melvinmajor/tfe-PiSense/doc/pi4-diagram2.jpg

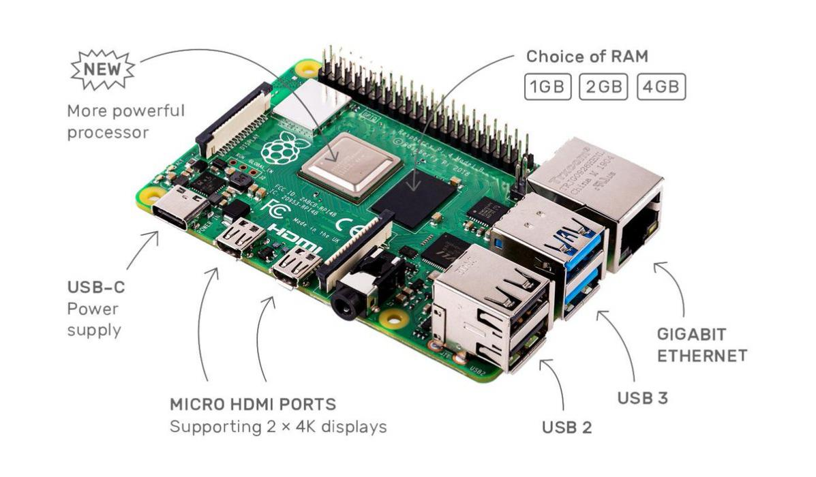
doc/pi4-diagram2.jpg
