melvinmajor/tfe-PiSense/doc/Pictures/3D-box-side1.png

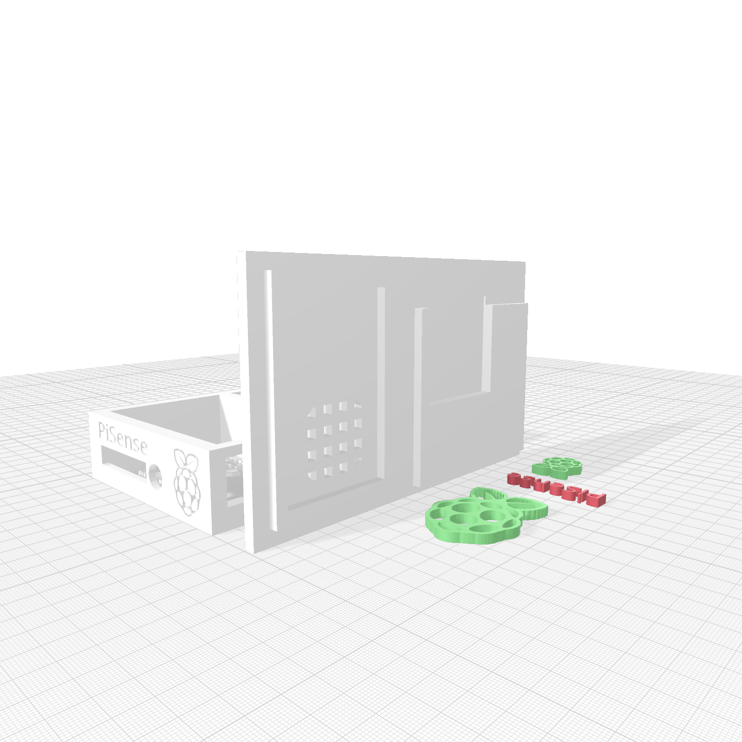
doc/Pictures/3D-box-side1.png
