melvinmajor/tfe-PiSense/doc/Pictures/3D-box-side2.png

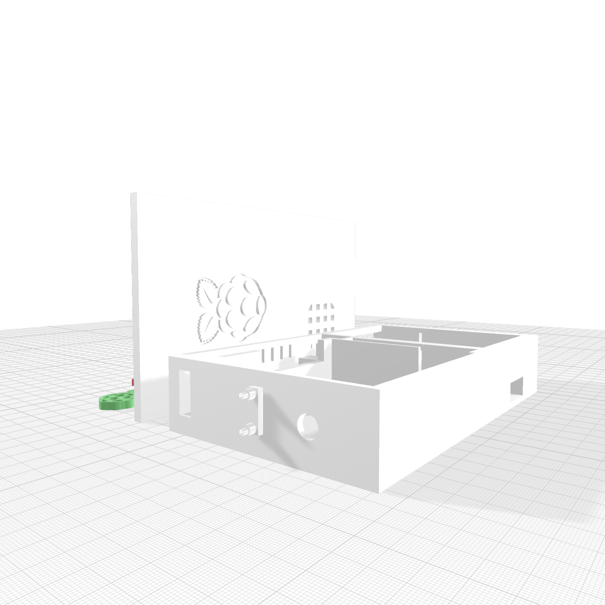
doc/Pictures/3D-box-side2.png
