melvinmajor/tfe-PiSense/doc/Pictures/web-platform-localhost.png

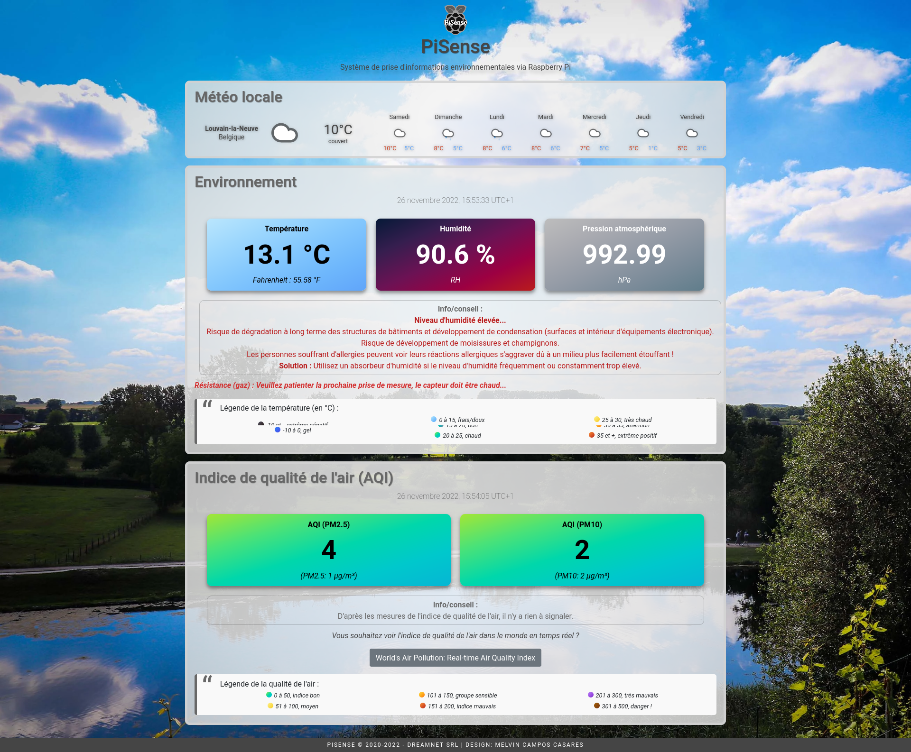
doc/Pictures/web-platform-localhost.png
