melvinmajor/tfe-PiSense/doc/SSL_Labs+Security_headers/securityheaders-june16-camposcasares.be.png

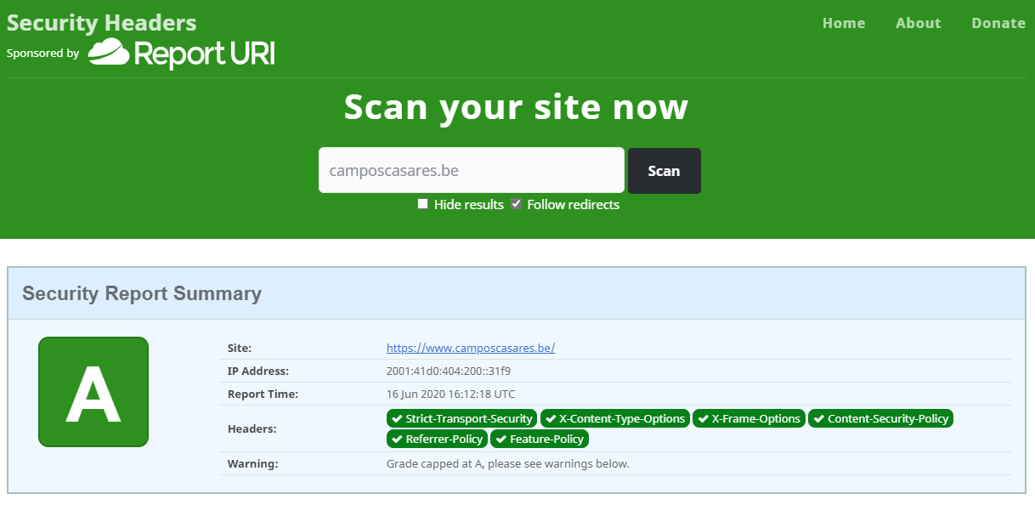
doc/SSL_Labs+Security_headers/securityheaders-june16-camposcasares.be.png
