melvinmajor/tfe-PiSense/localhost-web/assets/images/air-quality-index.webp

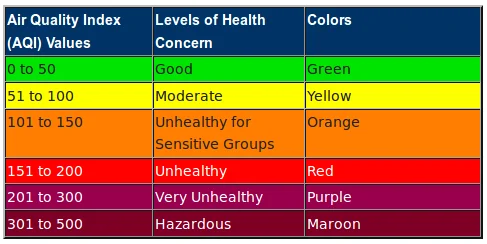
localhost-web/assets/images/air-quality-index.webp
