melvinmajor/tfe-PiSense/localhost-web/assets/images/background-v1.webp

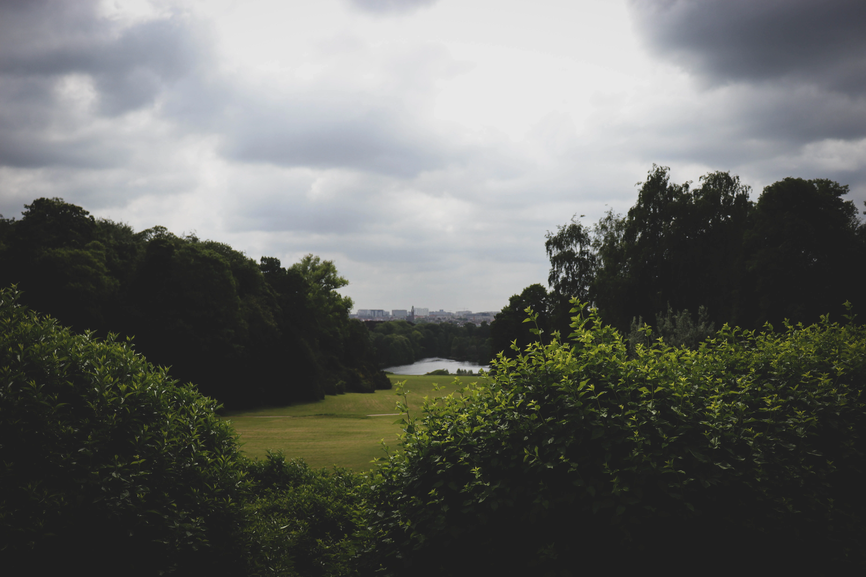
localhost-web/assets/images/background-v1.webp
