melvinmajor/tfe-PiSense/localhost-web/assets/images/background.webp

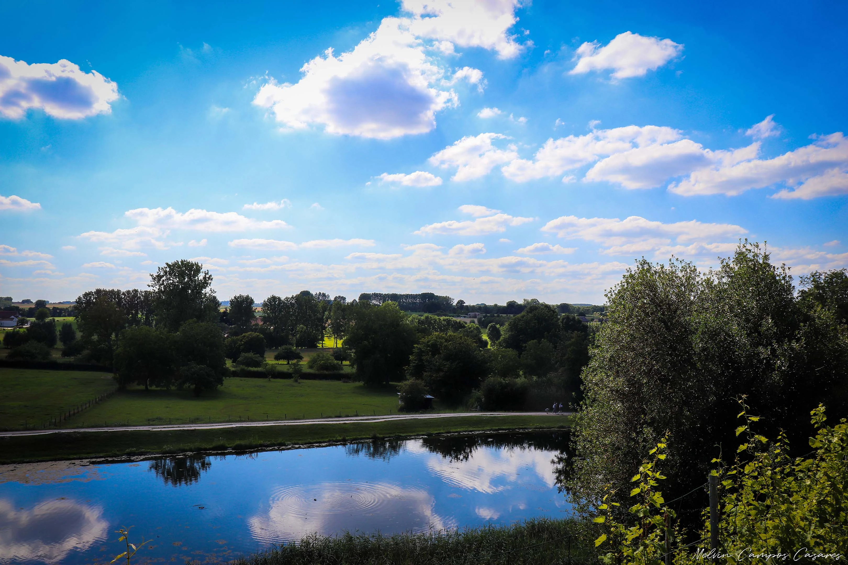
localhost-web/assets/images/background.webp
