melvinmajor/tfe-PiSense/config-manual/Connect-sensors.pdf

# PiSense

## Manual connect sensors on Raspberry Pi devices

## Melvin Campos Casares


9 june 2019

PiSense | 9 june 2019

## Manual - how to connect the different sensors onto Raspberry Pi devices

1 Connect one or multiple sensors onto Raspberry Pi devices | 3
Manual - connect sensors on Raspberry Pi devices | 2

## 1 Connect one or multiple sensors onto Raspberry Pi devices

Currently, this project support the following sensors:

- Nova SDS011: Fine particles in suspension (PM2.5, PM10).
- Bosch BMP280 (based on Adafruit library): temperature and humidity.
- Bosch BME280 (based on Adafruit library): temperature, humidity, atmospheric pressure.
- Bosch BME680 (based on Pimoroni library): temperature, humidity, gas (TVOC, eCO2), atmospheric pressure.

If for any reason you need to connect one of the sensors, here you will find a diagram to help you find out how to process it.

As it’s meant to be connected on Raspberry Pi devices (this project is working on such device), take the board of the Raspberry in front of you with the GPIO connectivity port at your upper right side. Like that, the diagram will correspond to your GPIO port.

### 1.1 Nova SDS011 sensor

For this sensor, we are using the included Serial to USB adapter.

- Simply connect the cable on the SDS011 module on one side,
- On the other side, connect the cable on the USB adapter,
- Connect the adapter on one of the USB ports available on your Raspberry Pi device.
- You are done.

### 1.2 Bosch BMP280 sensor

Figure 1: Bosch BMP280 sensor GPIO connect diagram

### 1.3 Bosch BME280 sensor

Figure 2: Bosch BME280 sensor GPIO connect diagram

### 1.4 Bosch BME680 sensor

Figure 3: Bosch BME680 sensor GPIO connect diagram
